diminDDL/ProPico/outputs/blender/front_render.png

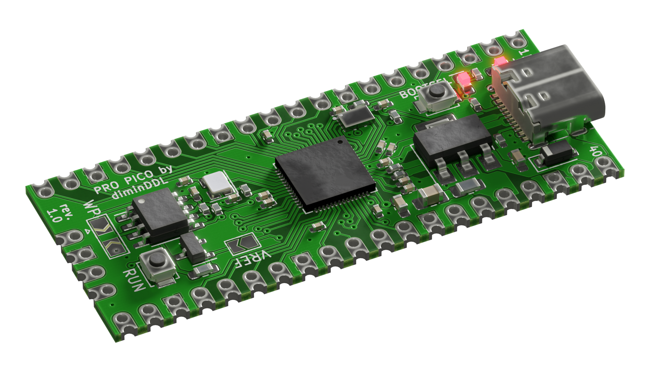
outputs/blender/front_render.png
