diminDDL/ProPico/outputs/blender/bootm_render.png

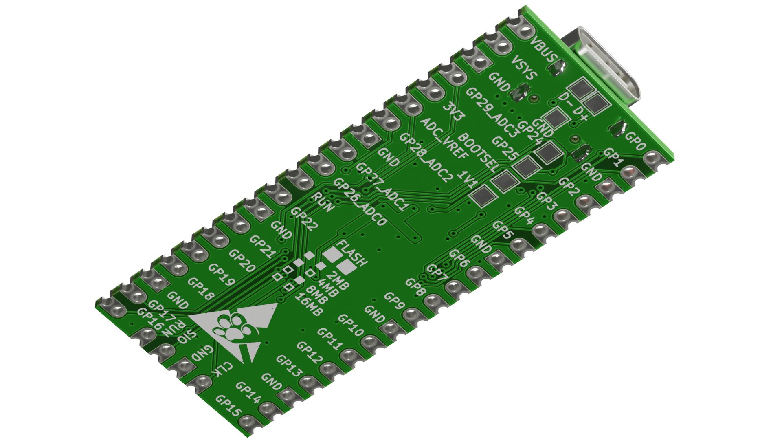
outputs/blender/bootm_render.png
